dsandall/pico2-knob/mechanical/pico2_housing-v2shell_lower.step

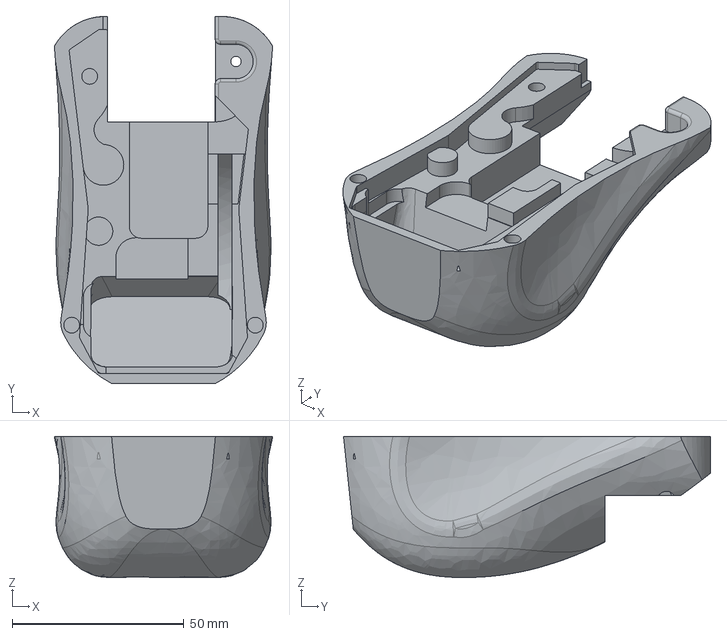
[picture p15: CAD file, 2026-09-07]
mechanical/pico2_housing-v2shell_lower.step
63.6 x 106.9 x 41.1 mm
