dsandall/pico2-knob/mechanical/stencil/pico2-knob-EdgeCuts.dxf

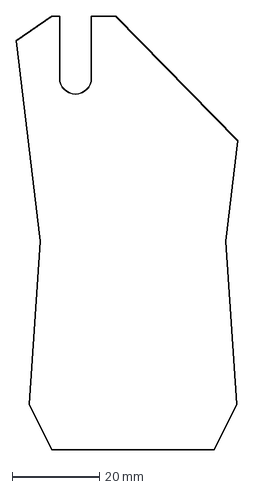
[picture p16: CAD file, 2026-09-07]
mechanical/stencil/pico2-knob-EdgeCuts.dxf
51.0 x 99.5 mm
