dsandall/pico2-knob/mechanical/pcb_nubbin_mount.FCStd

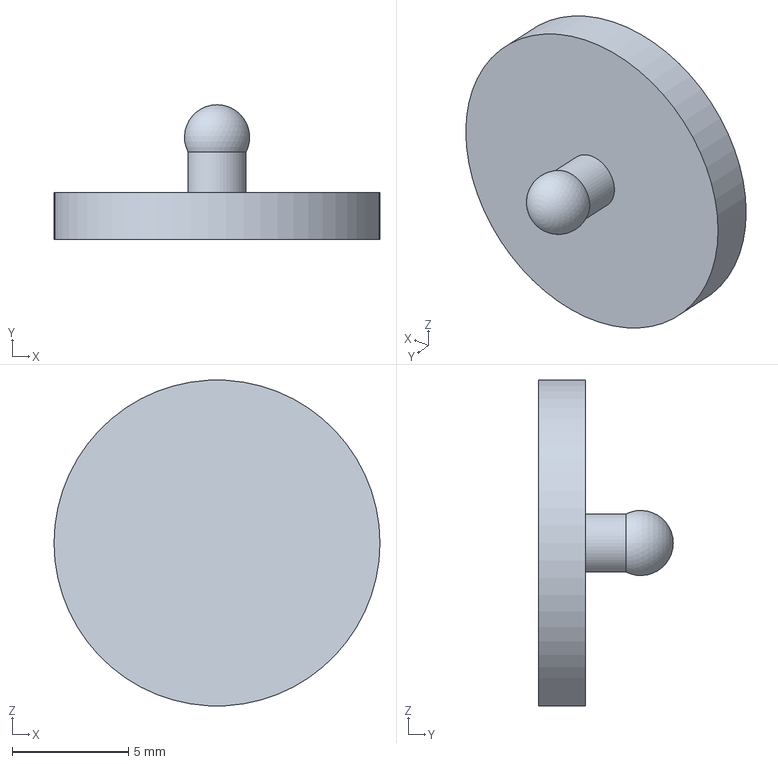
[picture p17: CAD file, 2026-09-05]
mechanical/pcb_nubbin_mount.FCStd
14.0 x 5.78 x 14.0 mm
