dsandall/pico2-knob/mechanical/stencil/pico2-knob-PasteTop.dxf

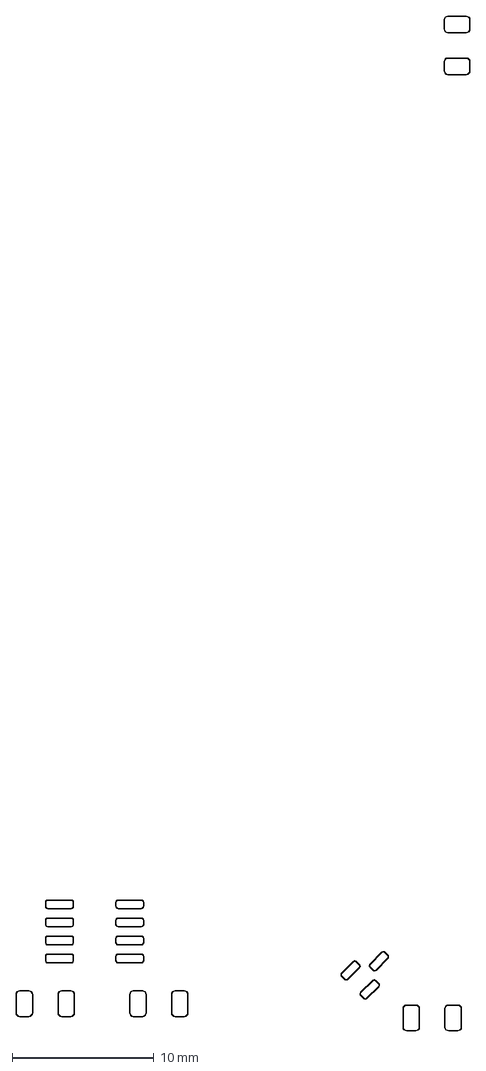
[picture p18: CAD file, 2026-09-07]
mechanical/stencil/pico2-knob-PasteTop.dxf
32.0 x 71.5 mm
